chrisstubbs93/Doorbell_PCB/Arduino/Doorbell/Web.ino

/**
    \file Web.ino
    Handles WiFi access point, WiFi client, DNS server, webservers for initial setup wizard and configuration, IFTTT integration.
    Also contains all HTML for webservers
*/

const IPAddress apIP(192, 168, 1, 1); //!< Fixed IP address of device for setup wizard in AP mode.
const char* apSSID = "_SETUP"; //!< Name of SSID for setup wizard access point.
String ssidList; //!< List of all detected SSIDs from scan.

/*! Run background WiFi DNS server and webserver tasks. */
void wifiTasks() {
  if (settingMode) {
    dnsServer.processNextRequest();
  }
  webServer.handleClient();
}

/*! Send a webhooks request to IFTTT with the room name and appropraite lecturers key. Display status on screen. Input = 0...7. */
void ring(const int bus)
{
  lastPressed = millis(); //record the button was pressed for sleep mode
  if (lecturerStatus[bus] == "Available") {
    digitalWrite(LEDAVAILPIN, HIGH);
  } else {
    digitalWrite(LEDBUSYPIN, HIGH);
  }
  if (lecturerStatus[bus] == "Available" or busyNotif)
  {
    display.setRotation(1);
    display.fillScreen(GxEPD_WHITE);
    display.setTextColor(GxEPD_BLACK);
    display.setFont(font);
    display.setCursor(0, 16 * 4);
    display.print("Contacting "); display.print(lecturerNames[bus]); display.println("...");
    display.update();
    if ((WiFi.status() == WL_CONNECTED)) {
      HTTPClient http;
      Serial.println((String)"[INFO] HTTP Req: https://maker.ifttt.com/trigger/" + room + "/with/key/" + lecturerIFTTkeys[bus]);
      http.begin((String)"https://maker.ifttt.com/trigger/" + room + "/with/key/" + lecturerIFTTkeys[bus]);
      int httpCode = http.GET();
      if (httpCode > 0) {
        String payload = http.getString();
        Serial.println((String)"[INFO] httpCode: " + httpCode);
        Serial.println((String)"[INFO] payload: " + payload);
        if (httpCode != 200) {
          //Error communicating with IFTTT service.
          if (httpCode == 302) {
            //"Temporarily moved" (common error for no key)
            errorMsg("Error communicating with \nIFTTT.\n\nDid you set the room and\nlecturer key?");
          }
          errorMsg("Error communicating with IFTTT " + (String)httpCode + " " + payload);
          errorMsg("Req: " + (String)"https://maker.ifttt.com/trigger/" + room + "/with/key/" + lecturerIFTTkeys[bus]);
        }
        if (httpCode == 200) {
          //success
          digitalWrite(LEDOKPIN, HIGH);
          display.setRotation(1);
          display.fillScreen(GxEPD_WHITE);
          display.setTextColor(GxEPD_BLACK);
          display.setFont(font);
          display.setCursor(0, 16 * 4);
          if (lecturerStatus[bus] == "Available") {
            display.println(wordWrap(lecturerNames[bus] + " has been notified."));
          } else {
            display.println(wordWrap(lecturerNames[bus] + " has been notified, but may be busy."));
          }
          display.update();
        }
      }
      else {
        errorMsg("Unknown error in HTTP request.");
      }
      http.end(); //Free the resources
    } else {
      errorMsg("Wifi not connected. Restarting in 30 seconds.");
      delay(30000);
      ESP.restart();
    }
    delay(5000);
    digitalWrite(LEDOKPIN, LOW);
    digitalWrite(LEDAVAILPIN, LOW);
    digitalWrite(LEDBUSYPIN, LOW);
    writeNames();
  } else {
    display.setRotation(1);
    display.fillScreen(GxEPD_WHITE);
    display.setTextColor(GxEPD_BLACK);
    display.setFont(font);
    display.setCursor(0, 16 * 4);
    display.println(wordWrap((String)lecturerNames[bus] + " is busy/away."));
    display.println("Please try again later.");
    display.update();
    delay(3000);
    digitalWrite(LEDOKPIN, LOW);
    digitalWrite(LEDAVAILPIN, LOW);
    digitalWrite(LEDBUSYPIN, LOW);
    writeNames();
  }
}

/*! Attempt to connect to specified WiFi SSID. After 3 failures, default to setup wizard. */
boolean connectWiFi() {
  int connAttempts = 0;
  while (connAttempts < 3) {
    connAttempts++;
    if (EAP_IDENTITY == "") {
      //if wpa2-psk is configured
      Serial.println((String)"[INFO] WPA2-PSK mode.");
      WiFi.begin(ssid.c_str(), rot(wifipsk).c_str());
    } else {
      //if eduroam  is configured
      Serial.println((String)"[INFO] WPA2-Enterprise mode.");
      WiFi.disconnect(true);
      WiFi.mode(WIFI_STA);
      const unsigned char* EAP_IDENTITY_A = reinterpret_cast<const unsigned char *>( rot(EAP_IDENTITY).c_str() ); //convert strings to unsigned char for enterprise functions
      const unsigned char* EAP_PASSWORD_A = reinterpret_cast<const unsigned char *>( rot(EAP_PASSWORD).c_str() );
      esp_wifi_sta_wpa2_ent_set_username(EAP_IDENTITY_A, strlen(rot(EAP_IDENTITY).c_str())); //set enterprise wifi parameters
      esp_wifi_sta_wpa2_ent_set_password(EAP_PASSWORD_A, strlen(rot(EAP_PASSWORD).c_str()));
      esp_wpa2_config_t config = WPA2_CONFIG_INIT_DEFAULT(); //set config settings to default
      esp_wifi_sta_wpa2_ent_enable(&config); //enable enterprise mode
      WiFi.begin(ssid.c_str(), rot(wifipsk).c_str()); //connect to AP
    }
    Serial.print("[INFO] Connecting to " + ssid + ". Attempt " + connAttempts);
    addToLog(ssid + " connecting");
    if (checkConnection()) {
      return true; //Connected OK.
    } else {
      //Connection failed. Try again.
      if (connAttempts == 3) {
        //Display last attempt error
        errorMsg("WiFi connection timed out.\nThis is attempt " + (String)connAttempts + "/3.\nAborting connection.\nEntering setup mode.");
      } else {
        //Display retry error
        errorMsg("WiFi connection timed out.\nThis is attempt " + (String)connAttempts + "/3.\nTrying again in 10s.\nPress [A] to retry now.\nPress [B] to run setup.");
        unsigned long tmr = millis();
        while ((millis() - tmr < 10000)) {
          if (digitalRead(BTNAPIN)) {
            //User requested retry
            if (connAttempts == 3) connAttempts = 2; //Manually allow one more try if on last try.
            break;
          }
          if (digitalRead(BTNBPIN)) {
            //User requested setup mode
            settingMode = true;
            return false;
          }
        }
      }
      settingMode = true;
    }
  }
  //Failed to connect after 3 attempts.
  return false;
}

/*! Check WiFi is connected. */
boolean checkConnection() {
  int count = 0;
  while ( count < 15 ) {
    if (WiFi.status() == WL_CONNECTED) {
      Serial.println("\n[INFO] Connected!");
      settingMode = false;
      return (true);
    }
    delay(500);
    Serial.print(".");
    count++;
  }
  Serial.println();
  return false;
}

/*! Start the appropriate web server depending on if the mode is normal or setup mode. */
void startWebServer() {
  if (settingMode) { //Set up webserver to serve captive portal for wifi setup wizard
    setupMsg(apSSID); //Display setup screen
    webServer.on("/settings", handleSettings);
    webServer.on("/eduroam", handleEduroam);
    webServer.on("/setap", handleSetAP);
    webServer.onNotFound(handleSetupRoot);
  }
  else { //Set up webserver to serve normal setup page
    Serial.print("[INFO] Starting Web Server at ");
    Serial.println(WiFi.localIP().toString());
    addToLog((String)"IP addr: " + WiFi.localIP().toString());
    webServer.on("/", handleRoot);
    webServer.on("/reset", handleReset);
    webServer.on("/savesettings.do", saveSettings);
    webServer.onNotFound(handleNotFound);
  }
  webServer.begin();
}

/*! Prepare and start the setup wizard with list of scanned SSIDs. */
void setupMode() {
  //Disconnect any connections and scan for AP's
  WiFi.mode(WIFI_STA);
  WiFi.disconnect();
  delay(100);
  int n = WiFi.scanNetworks();
  delay(100);
  Serial.println("");
  for (int i = 0; i < n; ++i) {
    ssidList += "<option value=\"";
    ssidList += WiFi.SSID(i);
    ssidList += "\">";
    ssidList += WiFi.SSID(i);
    ssidList += "</option>";
  }
  delay(100);
  //Create config AP
  WiFi.mode(WIFI_AP);
  delay(250);
  WiFi.softAPConfig(apIP, apIP, IPAddress(255, 255, 255, 0));
  delay(250);
  WiFi.softAP(apSSID);
  delay(250);
  dnsServer.setErrorReplyCode(DNSReplyCode::NoError);
  dnsServer.start(53, "*", apIP);
  Serial.println((String)"[INFO] DNS server started");
  startWebServer();
  Serial.println((String)"[INFO] Starting Access Point at " + apSSID);
}

/*! Generate basic HTML tags around content. */
String makePage(String title, String contents) {
  String s = "<!DOCTYPE html><html><head>";
  s += "<meta name=\"viewport\" content=\"width=device-width,user-scalable=0\">";
  s += "<title>Lecturer availability door announcer</title>";
  s += "<style> body { background-color: #cccccc; font-family: Arial, Helvetica, Sans-Serif; Color: #000088; } </style>";
  s += "</head><body>";
  s += contents;
  s += "</body></html>";
  return s;
}

/*! Replace URL encoded characters. */
String urlDecode(String input) {
  String s = input;
  s.replace("%20", " ");
  s.replace("+", " ");
  s.replace("%21", "!");
  s.replace("%22", "\"");
  s.replace("%23", "#");
  s.replace("%24", "$");
  s.replace("%25", "%");
  s.replace("%26", "&");
  s.replace("%27", "\'");
  s.replace("%28", "(");
  s.replace("%29", ")");
  s.replace("%30", "*");
  s.replace("%31", "+");
  s.replace("%2C", ",");
  s.replace("%2E", ".");
  s.replace("%2F", "/");
  s.replace("%2C", ",");
  s.replace("%3A", ":");
  s.replace("%3A", ";");
  s.replace("%3C", "<");
  s.replace("%3D", "=");
  s.replace("%3E", ">");
  s.replace("%3F", "?");
  s.replace("%40", "@");
  s.replace("%5B", "[");
  s.replace("%5C", "\\");
  s.replace("%5D", "]");
  s.replace("%5E", "^");
  s.replace("%5F", "-");
  s.replace("%60", "`");
  return s;
}

/*! Handle requests to the main page of the config interface. Check authentication and serve page with current variables. */
void handleRoot() {
  if (!webServer.authenticate(&www_username[0u], &www_password[0u])) {
    return webServer.requestAuthentication();
    webServer.send(200, "text/plain", "Login OK");
  }
  else {
    int sec = millis() / 1000;
    int min = sec / 60;
    int hr = min / 60;
    char timestamp [100];
    snprintf(timestamp, 100, "%02d:%02d:%02d", hr, min % 60, sec % 60);
    float VBAT = ((200.0f / 100.0f) * 3.30f * float(analogRead(BATTMONPIN)) / 4095.0f) + 0.2f; // LiPo battery
    int vbatt = (float)((100.0f / 4.2f) * VBAT);
    String temp = "<html>\
  <head>\
    <title>Lecturer availability door announcer</title>\
    <style>\
      body { background-color: #cccccc; font-family: Arial, Helvetica, Sans-Serif; Color: #000088; }\
    </style>\
  </head>\
  <body>\
    <h1>Lecturer availability door announcer</h1>\
    Final year BEng project by Chris Stubbs (2019)\
    <h2>Status</h2>\
    <p>Uptime: " + (String)timestamp + "</p>\
    <p>Battery: " + (String)vbatt + "%, " + (String)VBAT + "V</p>\
    <p>Free heap (RAM): " + ESP.getFreeHeap() + " bytes.</p>\
    <h2>Settings</h2>\
<form action='/savesettings.do' method='post'>\
Sensor threshold: <input name='threshold' type='text' value='" + (String)thres + "'>\
<br /><br />\
Notify lecturer on ring even if they are busy?: <input name='busyNotif' type='checkbox'" + ((busyNotif) ? (" checked") : ("")) + ">\
<br /><br />\
Enable power saving sleep mode after <input name='sleepDelay' type='text' value='" + sleepDelay + "'> mins?: <input name='powerSave' type='checkbox'" + ((powerSave) ? (" checked") : ("")) + ">\
<br /><br />\
Room name: <input name='room' type='text' value='" + room + "'>\
<br /><br />\
Admin password: <input name='adminpw' type='text' value='" + www_password + "'>\
<br /><br />\
<table width='500'>\
  <tr>\
    <td>&nbsp;</td>\
    <td>Lecturer 1</td>\
    <td>Lecturer 2</td>\
    <td>Lecturer 3</td>\
    <td>Lecturer 4</td>\
    <td>Lecturer 5</td>\
  </tr>\
  <tr>\
    <td>Name</td>\
    <td><input name='l1name' type='text' value='" + lecturerNames[0] + "'></td>\
    <td><input name='l2name' type='text' value='" + lecturerNames[1] + "'></td>\
    <td><input name='l3name' type='text' value='" + lecturerNames[2] + "'></td>\
    <td><input name='l4name' type='text' value='" + lecturerNames[3] + "'></td>\
    <td><input name='l5name' type='text' value='" + lecturerNames[4] + "'></td>\
  </tr>\
  <tr>\
    <td>Key</td>\
    <td><input name='l1key' type='text' value='" + lecturerIFTTkeys[0] + "'></td>\
    <td><input name='l2key' type='text' value='" + lecturerIFTTkeys[1] + "'></td>\
    <td><input name='l3key' type='text' value='" + lecturerIFTTkeys[2] + "'></td>\
    <td><input name='l4key' type='text' value='" + lecturerIFTTkeys[3] + "'></td>\
    <td><input name='l5key' type='text' value='" + lecturerIFTTkeys[4] + "'></td>\
  </tr>\
  <tr>\
    <td>Status</td>\
    <td>" + generateStatusDropdown(0) + "</td>\
    <td>" + generateStatusDropdown(1) + "</td>\
    <td>" + generateStatusDropdown(2) + "</td>\
    <td>" + generateStatusDropdown(3) + "</td>\
    <td>" + generateStatusDropdown(4) + "</td>\
  </tr>\
</table>\
<input type='submit' value='Save'>\
</form>\
<br /><br />\
<p><a href='/reset'>Reset all settings and run Wi-Fi setup</a></p>\
  </body>\
</html>";
    webServer.send(200, "text/html", temp);
  }
}

/*! Generate HTML for dropdown with status options. */
String generateStatusDropdown(uint8_t n) {
  //Generates the HTML string for a status dropdown of the given lecturer number (n).
  int num = n + 1;
  String tmphtml = "";
  tmphtml = "<select name='l" + (String)num + "status'>";

  tmphtml += "<option ";
  if (lecturerStatus[n] == "Available") tmphtml += "selected ";
  tmphtml += "value='Available'>Available</option>";

  tmphtml += "<option ";
  if (lecturerStatus[n] == "Away") tmphtml += "selected ";
  tmphtml += "value='Away'>Away</option>";

  tmphtml += "<option ";
  if (lecturerStatus[n] == "Busy") tmphtml += "selected ";
  tmphtml += "value='Busy'>Busy</option>";

  tmphtml += "<option ";
  if (lecturerStatus[n] == "") tmphtml += "selected ";
  tmphtml += "value=''></option>";

  return tmphtml;
}

/*! Save settings recieved from the web config interface to SPIFFS and load them into current memory. */
void saveSettings() {
  if (!webServer.authenticate(&www_username[0u], &www_password[0u])) {
    return webServer.requestAuthentication();
    webServer.send(200, "text/plain", "Login OK");
  }
  else {
    room = webServer.arg("room");
    busyNotif = (webServer.arg("busyNotif") == "on"); //true if checked
    powerSave = (webServer.arg("powerSave") == "on"); //true if checked
    thres = webServer.arg("threshold").toFloat();
    sleepDelay = webServer.arg("sleepDelay").toInt();
    www_password = webServer.arg("adminpw");
    lecturerNames[0] = webServer.arg("l1name");
    lecturerNames[1] = webServer.arg("l2name");
    lecturerNames[2] = webServer.arg("l3name");
    lecturerNames[3] = webServer.arg("l4name");
    lecturerNames[4] = webServer.arg("l5name");
    lecturerIFTTkeys[0] = webServer.arg("l1key");
    lecturerIFTTkeys[1] = webServer.arg("l2key");
    lecturerIFTTkeys[2] = webServer.arg("l3key");
    lecturerIFTTkeys[3] = webServer.arg("l4key");
    lecturerIFTTkeys[4] = webServer.arg("l5key");
    lecturerStatus[0] = webServer.arg("l1status");
    lecturerStatus[1] = webServer.arg("l2status");
    lecturerStatus[2] = webServer.arg("l3status");
    lecturerStatus[3] = webServer.arg("l4status");
    lecturerStatus[4] = webServer.arg("l5status");
    String out = "";
    out += "Saved!\n";
    out += "<a href='/'>Go back</a>\n";
    webServer.send(200, "text/html", out);
    saveConfig(); //commit new settings to config file
    writeNames(); //update the display
  }
}

/*! Serve error page if request is unhandled. */
void handleNotFound() {
  String message = "File Not Found\n\n";
  message += "URI: ";
  message += webServer.uri();
  message += "\nMethod: ";
  message += (webServer.method() == HTTP_GET) ? "GET" : "POST";
  message += "\nArguments: ";
  message += webServer.args();
  message += "\n";

  for (uint8_t i = 0; i < webServer.args(); i++) {
    message += " " + webServer.argName(i) + ": " + webServer.arg(i) + "\n";
  }
  webServer.send(404, "text/plain", message);
}

/*! Handle user request to reset settings and reboot device. */
void handleReset() {
  if (!webServer.authenticate(&www_username[0u], &www_password[0u])) {
    return webServer.requestAuthentication();
    webServer.send(200, "text/plain", "Login OK");
  }
  else {
    SPIFFS.remove("/config.json");
    String s = "<h1>Wi-Fi settings reset.</h1><p>The device will now restart.</p>";
    s += "<p>Scan for and connect to the Setup access point.</p>";
    s += "<p>You may now close this page.</p>";
    webServer.send(200, "text/html", makePage("Reset Wi-Fi Settings", s));
    delay(1000); //delay to finish serving the page before restart
    ESP.restart();
  }
}

/*! Serve main menu of setup wizard (WPA2-PSK / WPA2-ENTERPRISE). */
void handleSetupRoot() {
  String s = "<h1>Lecturer availability door announcer</h1>";
  s += "<p>Final year BEng project by Chris Stubbs (2019)</p>";
  s += "<p><a href=\"/settings\">Setup wizard for standard WiFi (WPA2)</a></p>";
  s += "<p><a href=\"/eduroam\">Setup wizard for eduroam (WPA2-Enterprise)</a></p>";
  webServer.send(200, "text/html", makePage("Setup Wizard", s));
}

/*! Serve menu for WPA2-PSK setup. */
void handleSettings() {
  String s = "<h1>Wi-Fi Settings</h1><p><a href=\"/\">Go back</a></p><p>Please enter settings for standard WiFi (WPA2).</p>";
  s += "<form method=\"get\" action=\"setap\">";
  s += "<table><tr>";
  s += "<td>SSID:</td><td><select name=\"ssid\">";
  s += ssidList;
  s += "</select></td></tr><td>Password:</td><td><input name=\"pass\" length=64 type=\"password\"></td></tr>";
  s += "<tr><td><input type=\"submit\"></td></tr></table></form>";
  webServer.send(200, "text/html", makePage("Wi-Fi Settings", s));
}

/*! Serve menu for WPA2-ENTERPRISE setup. */
void handleEduroam() {
  String s = "<h1>Wi-Fi Settings</h1><p><a href=\"/\">Go back</a></p><p>Please enter settings for eduroam (WPA2-Enterprise).</p><p>Password is typically left blank.</p><p>EAP Identity is typically your university email address.</p><p>EAP Password is typically your university password.</p>";
  s += "<form method=\"get\" action=\"setap\">";
  s += "<table><tr>";
  s += "<td>SSID:</td><td><select name=\"ssid\"><option selected value=\"eduroam\">eduroam</option>";
  s += ssidList;
  s += "</select></td></tr><td>Password:<?td><td><input name=\"pass\" length=64 type=\"password\"></td></tr>";
  s += "<tr><td>EAP Identity:</td><td><input name=\"eapidentity\" length=64></td></tr>";
  s += "<tr><td>EAP Password:</td><td><input name=\"eappass\" length=64 type=\"password\"></td></tr>";
  s += "<tr><td><input type=\"submit\"></td></tr></table></form>";
  webServer.send(200, "text/html", makePage("Wi-Fi Settings", s));
}

/*! Save settings from setup wizard and restart to use them. */
void handleSetAP() {
  ssid = urlDecode(webServer.arg("ssid"));
  wifipsk = rot(urlDecode(webServer.arg("pass")));
  EAP_IDENTITY = rot(urlDecode(webServer.arg("eapidentity")));
  EAP_PASSWORD = rot(urlDecode(webServer.arg("eappass")));
  saveConfig();

  String s = "<h1>Setup complete.</h1><p>Device will be connected to \"";
  s += ssid;
  s += "\" after the restart.</p>";
  s += "<p>Check the IP address displayed on the device and access this page from your web browser to continue the setup process.</p>";
  s += "<p>The username and password for the settings portal will be " + www_username + "/" + www_password + ".</p>";

  s += "<p>You may now close this page.</p>";
  webServer.send(200, "text/html", makePage("Wi-Fi Settings", s));
  delay(1000); //delay to finish serving the page before restart
  ESP.restart();
}
