chrisstubbs93/Doorbell_PCB/Arduino/Doorbell/bitmaps.h

/**
    \file bitmaps.h
    Stores bitmap images for display in program memory
*/

#if defined(ESP8266) || defined(ESP32)
#include <pgmspace.h>
#else
#include <avr/pgmspace.h>
#endif

/*! The LSBU logo stored as an array. */
/*! Generated from http://javl.github.io/image2cpp/ */
/*! Invert colours. */
const unsigned char BmpLSBU [] PROGMEM = {
  // LSBU Crest_simple white text_Horizon_BlackOutline, 296x128px
  0x00, 0x00, 0x00, 0x00, 0x60, 0x00, 0x00, 0x00, 0x0c, 0x00, 0x00, 0x00, 0x00, 0x00, 0x00, 0x00, 
  0x00, 0x00, 0x00, 0x00, 0x00, 0x00, 0x00, 0x00, 0x00, 0x00, 0x00, 0x00, 0x00, 0x00, 0x00, 0x00, 
  0x00, 0x00, 0x00, 0x00, 0x00, 0x00, 0x00, 0x00, 0x30, 0x48, 0x00, 0x00, 0x00, 0x24, 0x30, 0x00, 
  0x00, 0x00, 0x00, 0x00, 0x00, 0x00, 0x00, 0x00, 0x00, 0x00, 0x00, 0x00, 0x00, 0x00, 0x00, 0x00, 
  0x00, 0x00, 0x00, 0x00, 0x00, 0x00, 0x00, 0x00, 0x00, 0x00, 0x00, 0x00, 0x00, 0x28, 0x44, 0x00, 
  0x00, 0x00, 0x44, 0x48, 0x00, 0x00, 0x00, 0x00, 0x00, 0x00, 0x00, 0x00, 0x00, 0x00, 0x00, 0x00, 
  0x00, 0x00, 0x00, 0x00, 0x00, 0x00, 0x00, 0x00, 0x00, 0x00, 0x00, 0x00, 0x00, 0x00, 0x00, 0x00, 
  0x00, 0x00, 0x40, 0x04, 0x00, 0x00, 0x00, 0x44, 0x44, 0x00, 0x00, 0x00, 0x00, 0x00, 0x00, 0x00, 
  0x00, 0x00, 0x00, 0x00, 0x00, 0x00, 0x00, 0x00, 0x00, 0x00, 0x00, 0x00, 0x00, 0x00, 0x00, 0x00, 
  0x00, 0x00, 0x00, 0x00, 0x00, 0x00, 0x01, 0x89, 0x84, 0x00, 0x00, 0x00, 0x42, 0x22, 0x00, 0x00, 
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
  0x3f, 0xff, 0x3f, 0xff, 0xe0, 0x7f, 0xfc, 0x0f, 0xff, 0x9f, 0xff, 0xf8, 0x00, 0x00, 0x00, 0x00, 
  0x00, 0x00, 0x00, 0x00, 0x00, 0x01, 0x09, 0x22, 0x11, 0xe6, 0xdf, 0xff, 0x74, 0x90, 0x10, 0x89, 
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
};
